tbardouille/MEG_biosignal_phantom/Results/Nov 24 Cross-site validation/Figures/ECD_CTF_D1vD9_Butterfly.png

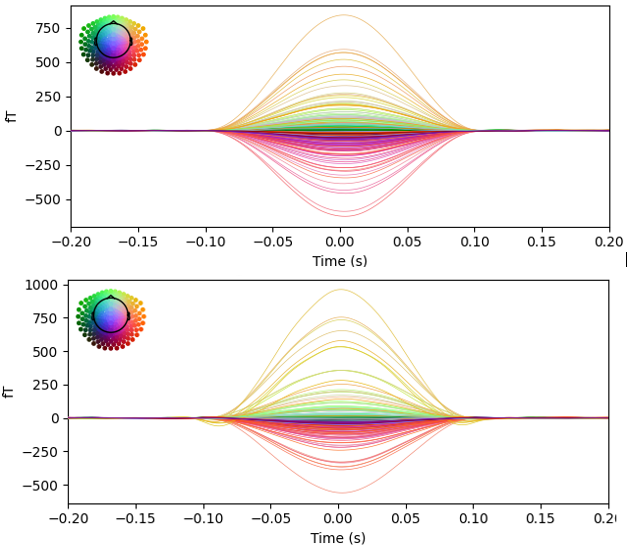
Results/Nov 24 Cross-site validation/Figures/ECD_CTF_D1vD9_Butterfly.png
