tbardouille/MEG_biosignal_phantom/Results/Nov 24 Cross-site validation/Figures/HPI_CTF_D1_Butterfly.png

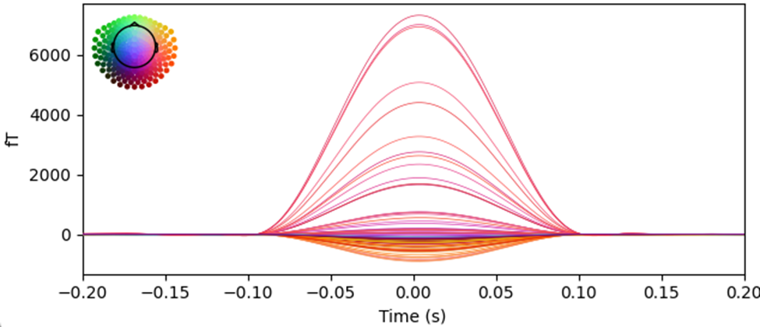
Results/Nov 24 Cross-site validation/Figures/HPI_CTF_D1_Butterfly.png
